WilgotW/rubik-s-robot/Algorithm/main.py

from uart import *
from solver import * 

def main():
    test_controller()
    # cube_colors = scan_all_faces()
    
    # if cube_colors:
    #     solve_command = solve_cube(cube_colors)
    #     if solve_command:
    #         send_rotation_commands(solve_command)

main()
